monroewilliams/trackball/pictures/prototype-1.jpeg

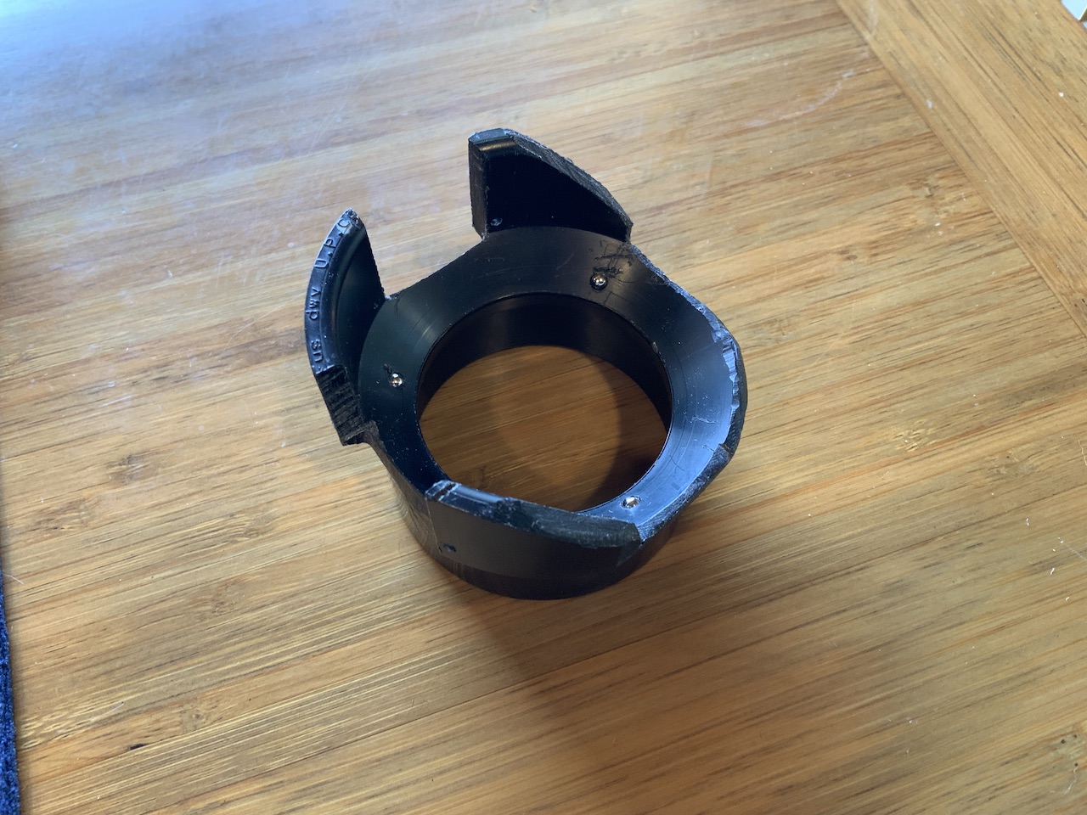
pictures/prototype-1.jpeg
