monroewilliams/trackball/hardware/trackball.scad

// This module prints the full trackball body, with all cutouts.
// full();

// This prints the bottom plate. To use it, comment out full() above and uncomment this line.
// The first argument is the thickness of the bottom cover in mm. I recommend at least 3, for structural integrity.
// The second argument controls whether the bottom cover includes the shape of the button supports.
// The third argument controls whether the attachment pins have screw holes for M3 countersunk machine screws.
//    This can be useful if the friction fit on the pins isn't holding well.
// bottom_cover(3, false, true);

////////////////////
// This selects the ball size.
// A regulation billiard ball is 2 1/4" (~57mm) in diameter.
// ball_diameter=57;

// Ball from the Kensington Slimblade is 55mm.
ball_diameter=55;

// A regulation snooker ball is 52.5mm (~2 1/16").
// The ball from a Trackman Marble FX is 52.33mm by my caliper
// The ball from an Elecom HUGE is 51.97mm by my caliper.
// ball_diameter=52.5;


////////////////////
// sensor_params sets the location and type of the sensors.
// Sensor params are:
// 0 - location angle (clockwise from top)
// 1 - sensor needs bottom access cutout (boolean)
// 2 - sensor type -- one of the following:
sensor_type_adns9800 = 0;
sensor_type_pmw3360 = 1;

sensor_params = [
    [180, true, sensor_type_pmw3360],
    [45, true, sensor_type_pmw3360]
];

////////////////////
// At one point, I found that having sensors directly face-on to the ball didn't work.
// This may have been due to some interaction between the ADNS9800 and the particular ball I was using.
// Setting this to 10 fixes the issues with that sensor/ball combination.
// With the pmw3360 and one of the purpose-made balls (Kensington/Perixx), it seems to work fine to have a skew angle of 0.
sensor_skew_angle=0;

// Should the attachment points have voids for screws?
bottom_screws = true;

////////////////////
// My custom designed pmw3360 boards need a little more clearance on the plug side.
// This should be harmless if using the boards from Tindie, but this lets you disable it
custom_pmw3360_clearance=true;

////////////////////
// True to have a cutout on the left side for cabling/access to the breadboard.
// This isn't needed with the new custom board, as the cable can exit to the front.
side_breadboard_cutout=true;

////////////////////
// If using the custom board, breadboard tabs aren't useful.
breadboard_tabs=true;

////////////////////
// This sets the number and location of the cutouts/supports for buttons.
// Button params are:
// 0 - azimuth angle (clockwise from top)
// 1 - elevation angle (downwards from level)
// 2 - distance from ball surface to button center (takes ball radius into account)
// 3 - tilt angle away from ball (additive with elevation angle)
// 4 - tilt angle in the clockwise direction
// 5 - cutout rotation
// 6 - front overhang (should match up with parametrs in microswitch_cherry_mx.scad)
// 7 - rear overhang (same)
// 8 - create bottom access cutout
// 9 - add support
example_button_params = [
    // main button (matches mircroswitch-cherry-mx-5-20.stl)
    [110, 27, 12, -5, 7, -3 - 90, 5, 20, true, false],

    // ring finger button (matches mircroswitch-cherry-mx-5-5.stl)
    [-70, 33, 13, 30, -8, 5, 0, 0, true, true],

    // second thumb button (matches mircroswitch-cherry-mx-20-0.stl)
    [165, 0, 17, 70, 60, 180 + 30, 20, 0, false, false],

    // middle finger button (could use mircroswitch-cherry-mx-5-5.stl or an actual keyswitch)
    [-25, 20, 17, -15, 30, 0, 0, 0, true, true],

    // index finger button (could use mircroswitch-cherry-mx-5-5.stl or an actual keyswitch)
    [10, -0, 17, 5, 30, 0, 0, 0, true, true],
];

button_params = [
    example_button_params[0],
    example_button_params[1],
    example_button_params[2]
];

////////////////////////////////////////////////////////////////
// Below this line, things get complicated. 

minimal_body_height=1;
minimal_body_diameter=67;

// Bearings are 1/8" == 3.175mm
ball_clearance=1;
bearing_diameter=3.175;

bottom_clearance=4;
hole_diameter=ball_diameter - 25;

bearing_angle=60;
bearing_spacing=[ 
    [0, 0, 0],
    [0, 0, 120],
    [0, 0, -120] 
];

sensor_angle=60;

sensor_clearance=2;
lens_thickness=3.3;
sensor_board_thickness=2;
sensor_board_clearance=0;
        

// Give the ball clearance all the way around in the recess
ball_radius=ball_diameter/2;
recess_radius=ball_radius + ball_clearance;

// Shorthand for the minimum z coordinate
bottom = -(recess_radius + bottom_clearance);

module button_transform(params)
{
    rotate([0, 0, params[0]])
    rotate([-params[1], 0, 0])
    translate([0, ball_radius + params[2], 0])
    rotate(-[params[3], 0, 0])
    rotate([0, params[4], 0])
    rotate([0, 0, params[5]]) 
    children();
}

button_pod_diameter = 20;

module ccube(x, y, z)
{
    translate([0, 0, z/2])
    cube(center=true, [x,y, abs(z)]);
}

module rcube(x, y, z, r)
{
    translate([0, 0, z < 0 ? z : 0])
    linear_extrude(height = abs(z))
    rrect(x, y, r);
}

module rrect(x, y, r)
{
    translate([-x/2, -y/2, 0])
    translate([r, r, 0])
    offset(r)
    square([x - (r * 2), y - (r * 2)]);
}

module prender(convexity = 1)
{
    // Render only in preview mode.
    // Using unconditional render() calls seems to cause my final render to fail

    if ($preview)
    {
        render(convexity)
        children();
    }
    else
    {
        children();
    }
}

module shadow_hull(extra_height = 0)
{
    // This creates an object which is a hull of the object itself and its shadow on the x/y plane.
    hull()
    {
        // the child object
        children();

        // the projection of the child object
        translate([0, 0, bottom - 1 - extra_height]) 
        linear_extrude(height=1)
        projection()
        children();
    }
}

module ball()
{
    color("red")
    sphere(d=ball_diameter);
}

module ball_cutout()
{
    union()
    {
        // spherical part of the recess
        sphere(d=50);
        sphere(d=ball_diameter + (ball_clearance * 2));

        // clearance cut for ball removal, roughly matching the angle of the right front cut
        // The angle here isn't critical, it just needs to not look funny,
        // and not intersect the bearing cutouts (they have very tight tolerances)
        rotate([0, -45 , 30])
        rotate([0, 90, 0])
        cylinder(d=ball_diameter + (ball_clearance), h=ball_diameter);


        // bottom hole
        translate ([0, 0, -100])
        cylinder(h=100, d = hole_diameter);
    }
}

module bearing_cutouts()
{
    union()
    {
        // bearing holes
        for(i = bearing_spacing )
        {
            rotate(i)
            rotate([bearing_angle - 180, 0, 0])
            {
                new_bearing_holes = true;

                // Orginal bearing hole consists of a hemisphere and a straight cylinder.
                hull() 
                {
                    translate ([0,0,ball_radius + (bearing_diameter/2)])
                        sphere (d=bearing_diameter);
                    if (!new_bearing_holes)
                    {
                        // new bearing hole leaves the slight overhang, but makes cuts around it below.
                        translate ([0,0,ball_radius - (bearing_diameter/2)])
                        cylinder (h=bearing_diameter, d=bearing_diameter);
                    }
                }

                if (new_bearing_holes)
                {
                    // relief around the bearing hole - testing a different idea
                    cut_angle = 60;
                    translate([0,0,ball_radius + (bearing_diameter)])
                    for (i = [0, 120, 240])
                    rotate([0, 0, i + 90 - (cut_angle/2)])
                    rotate_extrude(cut_angle)
                    polygon([
                        [0, 0],
                        [0, -bearing_diameter],
                        [-bearing_diameter, -bearing_diameter]
                    ]);
                }

                // through-hole to push out the bearing
                cylinder (h=ball_radius + bearing_diameter + 100, d=2);
            }
        }
    }
}

module button_cutout(front_overhang = 0, rear_overhang = 0)
{
    union() 
    {
        translate([0, 0, -10])
        {
            // the hole the switch fits into
            ccube(14, 14, 20);
        }

        if ((front_overhang == 0) && (rear_overhang == 0))
        {
            // 3mm cut around the hole for seating/overhang and keycap
            rcube(20, 20, 20, 1);
        }
        else
        {
            // 1mm cut around the hole for seating/overhang
            ccube(16, 16, 20);
        }

        // Front and rear overhangs are intended to match up with the overhang parameters in 
        // microswitch-cherry-mx.scad.
        if (front_overhang > 0)
        {
            // Cutout for the safety catch
            translate([-7.5, 7, 0])
            cube([15, 5, 20]);
            // Cutout for the part of the top which extends past the catch
            translate([-7.5, 7, 4])
            cube([15, front_overhang + 3, 16]);
        }

        if (rear_overhang > 0)
        {
            translate([-7.5, -7 - (1 + rear_overhang), 0])
            cube([15, 1 + rear_overhang, 20]);
        }
    }
}

module button_access_base()
{
    translate([0, 0, -10])
    {
        ccube(14, 14, 1);
    }
}


adns9800_board_radius = 32;

// The pmw3360 board is 28mm wide, but the lens assembly is not quite centered on it.
// Either offset it slightly with pmw3360_board_offset or add a little extra width
// and let the size of the holes take up the slop.
pmw3360_board_width = 28 + 1;
pmw3360_board_offset = 0;
pmw3360_board_height = 21 + 1;
pmw3360_lens_radius = 7;
pmn3360_curved_top_scale = 0.25;

module sensor_screw_hole()
{
    // the screw hole
    translate([0, 0,-4])
    color("white", 0.5)
    // my original unknown-source self-tapping screws
    // cylinder(d=1.5, h=10);
    // 2mm machine screws
    cylinder(d=2, h=10);


    // screwdriver access
    translate([0, 0,-104])
    color("white", 0.5)
    cylinder(d=3, h=100);
}

module pmw3360_board()
{
    z = sensor_board_thickness + sensor_board_clearance;
    if (custom_pmw3360_clearance)
    {
        // Outline of the custom sensor board
        // a polygon with the shape of the new board
        x = pmw3360_board_width / 2;
        y = pmw3360_board_height / 2;
        color("green", 0.5)                     
        linear_extrude(height = z, center = false)
        polygon([
            [-x, -y],
            [-x, y],
            [x, y],
            [x, -y],
            [7, -y],
            [5.5, -(y + 2)],
            [-5.5, -(y + 2)],
            [-7, -y],
        ]);
    } else {
        // The board itself (original)
        color("green", 0.5) ccube(pmw3360_board_width, pmw3360_board_height, z);
    }
}

module sensor_cutout(params)
{
    if (params[2] == sensor_type_adns9800)
    {
        union()
        {
            // origin of the sensor is at the surface of the lens, 
            // with the lens facing towards +z, and the "top" of the sensor (where the wires exit) towards +y
        
            // window portion of lens is roughly 11x9mm. This will make a window.
            color("white", 0.25)
            hull()
            {
                rcube(11, 9, 6, 2);
                // round the top to reduce bridging
                translate([0, 2.5, 0])
                scale([1, 0.5, 1])
                cylinder(d=11, h=6);
            }
                        
            // Lens portion of sensor is 22 x 20 mm, centered on the board
            color("gray", 0.5)
            intersection()
            {
                ccube(22,adns9800_board_radius, -(lens_thickness + 1));
                translate([0, 0, -(lens_thickness + 2)])
                cylinder(d=adns9800_board_radius, h=lens_thickness + 3);
            }
        
            // the board is a 32mm circle, ~2mm thick.
            // Add some thickness to the back to leave room for components, etc.
            z = sensor_board_thickness + sensor_board_clearance;
            translate([0,0,-(lens_thickness + z)])
            {
                // The board itself
                color("green", 0.5) cylinder(d=adns9800_board_radius, h=z);
                
                // Hemisphere for clearance
                difference()
                {
                    color("white", 0.25)
                    sphere(d=adns9800_board_radius);
                    
                    translate([0,0,1])
                    cylinder(d=adns9800_board_radius, h=17);
                }
            }
            
            // The screws are 27mm apart, on the centerline of the board.
            screw_distance=27;
            for(i = [ screw_distance/2,
                    -screw_distance/2 ] )
            {
                translate([i, 0, 0])
                sensor_screw_hole();
            }
        }
    }
    else if(params[2] == sensor_type_pmw3360)
    {
        union()
        {
            // origin of the sensor is at the surface of the lens, 
            // with the lens facing towards +z, and the "top" of the sensor (where the wires exit) towards +y
        
            // window portion of lens is roughly 11x9mm. This will make a window.
            color("white", 0.25)
            hull()
            {
                rcube(11, 9, 6, 2);
                // round the top to reduce bridging
                translate([0, 2.5, 0])
                scale([1, 0.5, 1])
                cylinder(d=11, h=6);
            }
            
            // Lens portion of sensor is 21.2 x 19 mm
            color("gray", 0.5)
            intersection()
            {
                rcube(22, 20, -(lens_thickness + 1), pmw3360_lens_radius);
                // translate([0, 0, -(lens_thickness + 2)])
                // cylinder(d=32, h=lens_thickness + 3);
                
            }

            // The board is shifted slightly relative to the lens
            translate([pmw3360_board_offset, 0, 0])
            {
                // leave room for the wire solder joints on the lens side
                // color("white", 0.25)
                translate([0, pmw3360_board_height/2, ])
                {
                    hull()
                    {
                        translate([0, -2, 0])
                        ccube(pmw3360_board_width, 4, -(lens_thickness + 1));

                        // Curved cut above the board to reduce bridging
                        translate([0, 0, -(lens_thickness)])
                        scale([1, pmn3360_curved_top_scale, 1])
                        cylinder(d=pmw3360_board_width, h=0.1);
                    }
                }

                // the board is a 28mm x 21mm rectangle, ~2mm thick.
                // Add some thickness to the back to leave room for components, etc.
                z = sensor_board_thickness + sensor_board_clearance;
                translate([0,0,-(lens_thickness + z)])
                {
                    pmw3360_board();

                    hull()
                    {
                        // Curved cut above the board to reduce bridging
                        color("white", 0.25)
                        translate([0, pmw3360_board_height/2, z])
                        scale([1, pmn3360_curved_top_scale, 1])
                        cylinder(d=pmw3360_board_width, h=0.1);
                        
                        // backside clearance (half cylinder)
                        difference()
                        {
                            color("white", 0.25)
                            rotate([0, 90, 0])
                            cylinder(center = true, d=pmw3360_board_height, h=pmw3360_board_width);
                            
                            translate([0,0,1])
                            ccube(pmw3360_board_width + 2, pmw3360_board_height + 2, 17);
                        }
                    }
                }
                
                // The screws are 24mm apart, on the centerline of the board.
                screw_distance=24;
                for(i = [ screw_distance/2,
                        -screw_distance/2 ] )
                {
                    translate([i, 0, 0])
                    sensor_screw_hole();
                }
            }
        }
    }
}

module sensor_access_base(params)
{
    // This is just the backside model, used to create an access hole.
    if (params[2] == sensor_type_adns9800)
    {
        // the board is a 32mm circle, ~2mm thick.
        // Add some thickness to the back to leave room for components, etc.
        z = sensor_board_thickness + sensor_board_clearance;
        translate([0,0,-(lens_thickness + z)])
        {
            // The board itself
            cylinder(d=adns9800_board_radius, h=z);
            
            // Hemisphere for clearance
            difference()
            {
                sphere(d=adns9800_board_radius);
                
                translate([0,0,1])
                cylinder(d=adns9800_board_radius, h=17);
            }
        }
    }
    else if(params[2] == sensor_type_pmw3360)
    {
        // the board is a 28mm x 21mm rectangle, ~2mm thick.
        // Add some thickness to the back to leave room for components, etc.
        z = sensor_board_thickness + sensor_board_clearance;
        translate([0,0,-(lens_thickness + z)])
        {
            // The board is shifted slightly relative to the lens
            translate([pmw3360_board_offset, 0, 0])
            {
                // The board itself
                pmw3360_board();
                // color("green", 0.5) ccube(pmw3360_board_width, pmw3360_board_height, z);
                
                hull()
                {
                    // Curved cut above the board to reduce bridging
                    color("white", 0.25)
                    translate([0, pmw3360_board_height/2, z])
                    scale([1, pmn3360_curved_top_scale, 1])
                    cylinder(d=pmw3360_board_width, h=0.1);

                    // backside clearance (half cylinder)
                    difference()
                    {
                        color("white", 0.25)
                        rotate([0, 90, 0])
                        cylinder(center = true, d=pmw3360_board_height, h=pmw3360_board_width);
                        
                        translate([0,0,1])
                        ccube(pmw3360_board_width + 2, pmw3360_board_height + 2, 17);
                    }
                }
            }
        }
    }
}

module sensor_shell(params)
{
    // A solid which completely encloses the sensor cutout/access cutout,
    // so it can be protected from the top.

    if (params[2] == sensor_type_adns9800)
    {
        // This is essentially the sphere defined by sensor_access_base, expanded by 2mm.
        z = sensor_board_thickness + sensor_board_clearance;
        translate([0,0,-(lens_thickness + z)])
        {
            sphere(d=adns9800_board_radius + 4);
        }
    }
    else if(params[2] == sensor_type_pmw3360)
    {
        // The backside clearance half-cylinder, extended to a full cylinder, and made 2mm larger
        z = sensor_board_thickness + sensor_board_clearance;
        translate([0,0,-(lens_thickness + z)])
        {
            // The board is shifted slightly relative to the lens
            translate([pmw3360_board_offset, 0, 0])
            {
                hull()
                {
                    // Curved cut above the board to reduce bridging
                    translate([0, 2 + pmw3360_board_height/2, z])
                    scale([1, pmn3360_curved_top_scale, 1])
                    cylinder(d=4 + pmw3360_board_width, h=0.1);

                    rotate([0, 90, 0])
                    cylinder(center = true, d=pmw3360_board_height + 4, h=pmw3360_board_width + 4);
                }
            }
        }
    }
}

module sensorpod(params)
{
    rotate([sensor_angle, 0, 0])
    translate([0, 0, -(lens_thickness + ball_radius + sensor_clearance)]) 
    {
        rotate([sensor_skew_angle, 0, 0])
        {
            if (params[2] == sensor_type_adns9800)
            {
                difference()
                {
                    cylinder(d=adns9800_board_radius, h=lens_thickness);
                    
                    translate([-17, 2, 0]) 
                    cube([adns9800_board_radius + 2, 20, lens_thickness]);
                }
            }
            else if(params[2] == sensor_type_pmw3360)
            {
                // The board is shifted slightly relative to the lens
                translate([pmw3360_board_offset, 0, 0])
                {
                    ccube(pmw3360_board_width, pmw3360_board_height, lens_thickness);
                }
            }
        }
    }
}

breadboard_size = [46.5, 34.75, 9.5];
breadboard_offset = [-5, -(ball_radius + 21.5)];

module breadboard_tab()
{
    hull()
    {
        ccube(5.0, 5.0, 6.5);
        translate([0, 0, 6.5])
        sphere(d=4);
    }
}

module breadboard_cutout()
{
    union()
    {
        // main body
        ccube(breadboard_size[0], breadboard_size[1], breadboard_size[2]);

        // clearance cutout
        intersection()
        {
            // ccube(breadboard_size[0], breadboard_size[1], 200);
            linear_extrude(height=80, scale=1.0)
            square(center=true, [breadboard_size[0], breadboard_size[1]]);

            // Tweak the location of the top of the cutout to make it a reasonable shell
            // Note that any adjustment to the body shape may require adjusting this.
            translate([4.0, 2.0, -4.0])
            translate([-breadboard_offset[0], -breadboard_offset[1], -bottom])
            body();

        }

        if (breadboard_tabs)
        {
            // connection tabs
            translate([0, breadboard_size[1] / 2, 0])
            breadboard_tab();
            translate([0, -breadboard_size[1] / 2, 0])
            breadboard_tab();
            translate([breadboard_size[0] / 2, 0, 0])
            breadboard_tab();
            translate([-breadboard_size[0] / 2, 0, 0])
            breadboard_tab();
        }

        if (side_breadboard_cutout)
        {
            // USB Cable clearance
            translate([0, 0, 4])
            rotate([0, -100, 0])
            cylinder(d=breadboard_size[1], h=50);
        }
    }
}

module breadboard_clearance()
{

}

module body_left_cut(inner_fillet = 20, outer_fillet = 0)
{
    union()
    {
        rotate([-10, 0, 10])
        translate ([3- ball_radius, 0, bottom])
        {
            radius = 120;
            downward_curve = 40;
            ledge_height = 20;
            // translate([radius, 0, -radius])
            // cylinder(r=radius, h=radius * 2);

            translate([0, 0, ledge_height])
            rotate([0, downward_curve, 0])
            translate([radius, 0, -ledge_height])
            rotate([0, 0, 90])
            rotate_extrude(angle=180)
            intersection()
            {
                union()
                {
                    // fillet
                    fillet_amount = 20;
                    offset(outer_fillet)
                    offset(-(inner_fillet + outer_fillet))
                    offset(inner_fillet)
                    translate([radius, ledge_height])
                    rotate([0, 0, -downward_curve])
                    translate([-radius, -ledge_height])
                    union()
                    {
                        // upright wall
                        translate([-100, -100])
                        square([100 + radius, 200]);

                        // ledge
                        translate([radius, ledge_height])
                        rotate([0, 0, -15])
                        translate([-radius, -ledge_height])
                        translate([0, -100])
                        square([radius + 25, 100 + ledge_height]);

                        // Make outside edge vertical
                        translate([0, -107])
                        square([radius + 25, 100 + ledge_height]);

                    }

                    // offset(fillet_amount)
                    // offset(-fillet_amount) 
                    // square([50, 50]);
                }
                // Clip to positive X
                translate([0, -150])
                square([300, 300]);
            }
        }  
        // Don't cut anything aft of tail_y_boundary with this shape.
        // translate([-100, -200 + tail_y_boundary, -100])
        // cube([200, 200, 200]);
    }
}

module body_right_front_cut()
{
    scale([0.89, 0.9, 0.815])
    rotate([0, 0, 90])
    rotate_extrude(angle=-180)
    intersection()
    {
        // scale([0.8, 0.6])
        circle(r=100);

        // Clip to positive X
        translate([0, 0])
        square([300, 300]);
    }
}

module body_right_rear_cut_template(params)
{
    // Match the front right cut at the intersection point at the z=0 plane
    rotate([-params[2], 0, 0])
    scale([1, 1, 1.0 / params[3]])
    rotate([-90, 0, 0])
    {
        translate([-params[0], -params[1], 0])
        body_right_front_cut();
    }

}

module body_right_rear_cut(params)
{
    translate([params[0], params[1], 0])
    scale([1.0, params[3], 1.0])
    rotate([-params[2], 0, 0])
    union()
    {
        rotate_extrude()
        intersection()
        {  
            offset(-params[6]) 
            offset(params[6])
            union()
            {
                // Match the front right cut at the intersection point
                projection(cut=true)
                body_right_rear_cut_template(params);

                // add the horizontal base
                rotate([0, 0, -(params[2] + params[4])])
                translate([0, -100 + params[5]])
                square([250, 100]);
            }

            // Clip to positive X
            translate([0, -150])
            square([300, 300]);
        }
        
        // Don't clip forward of this part
        translate([-200, 0, -200])
        cube([400, 400, 400]);
    }
}

module body_right_cut_translation()
{
    y_translation_angle = -45;
    z_translation_angle = 40;
    translation_amount = 80 - ball_diameter / 4;

    rotate([0, -y_translation_angle, 0])
    rotate([0, 0, -z_translation_angle])
    translate([0, 0, -translation_amount])
    rotate([0, 0, z_translation_angle])
    rotate([0, y_translation_angle, 0])
    translate([0, -30, 0])
    children();
}

// right rear shape params are:
// 0 - x offset
// 1 - y offset
// 2 - saddle rotation angle
// 3 - y scaling
// 4 - horizontal component angle (added to saddle angle)
// 5 - horizontal component height
// 6 - fillet amount
// right_rear_params = [20, 0, 35, 0.6, 5.0, 26, 60];
// right_rear_params = [20, 0, 27, 0.7, 7.5, 30, 90];
right_rear_params = [21, 2, 25, 0.7, 8, 30, 90];
// Settings roughly equivalent to previous:
// right_rear_params = [28, 0, 0, 0.7, 5.1, 22.5, 70];
module body_right_cut()
{
    body_right_cut_translation()
    intersection()
    {
        union()
        {
            body_right_front_cut();

            // Don't cut left of the center point
            translate([-200, 0, 0])
            cube([200, 200, 200]);

            // and don't cut off the tail tip
            // translate([-100, -200 - 50, -100])
            // cube([200, 200, 200]);
        }
        union()
        {
            body_right_rear_cut(right_rear_params);
        }

    }
}

module body_button_supports()
{
    for(i = button_params )
    {
        if(i[9])
        {
            shadow_hull(10)
            button_transform(i)
            translate([0, 0, -10])
            rcube(20, 20, 10, 3);
        }
    }
}


module body(include_button_supports = true, include_sensor_shells = true)
{
    intersection()
    {
        // Clip to above bottom surface
        translate ([0, 0, bottom])
        ccube(400, 400, 400);

        body_unclipped(include_button_supports, include_sensor_shells);
    }

}
module body_unclipped(include_button_supports = true, include_sensor_shells = true)
{
    difference()
    {
        union()
        {
            intersection()
            {
                // left cut
                body_left_cut();
                        
                // right cut
                body_right_cut();
            }        
 
            if (include_button_supports)
            {
                body_button_supports();
            }

            if (include_sensor_shells)
            {
                sensor_shells();
            }
        }

        // Trim the front of the body so it's not pointy for no reason
        rotate([0, 0, 45])
        translate([0, 100, -100 + bottom])
        ccube(100, 100, 200);
    }
}

stud_diameter = 5;
stud_height = 2;

module bottom_stud()
{
    translate([0, 0, -0.01])
    cylinder(d=stud_diameter, h = stud_height + 0.01);
}

module bottom_stud_screw_hole()
{
    // Add a hole that can be used for an M3x8 countersunk screw, for more permanent installs.
    translate([0, 0, 2])
    {
        cylinder(d=3, h = 10);

        mirror([0, 0, 1])
        {
            linear_extrude(height=2, scale=2)
            circle(d=3);

            translate([0, 0, 2])
            linear_extrude(height=10)
            circle(d=6);
        }
    }
}


 module circle_outer(radius,fn)
 {
   fudge = 1/cos(180/fn);
   circle(r=radius*fudge,$fn=fn);
}

module bottom_stud_hole()
{
    union()
    {
        // Polygonal, circumcribed hole.
        hole_sides = 8;
        translate([0, 0, -0.01])
        linear_extrude(height=stud_height+0.02)
        circle_outer(stud_diameter/2, hole_sides);

        // Taper to a point for easier printing
        translate([0, 0, stud_height])
        linear_extrude(height=stud_diameter / 2, scale=0)
        circle_outer(stud_diameter/2, hole_sides);

        if (bottom_screws)
        {
            // Add a hole that can be used for an M3x8 countersunk screw, for more permanent installs.
            // height is the screw depth minus the bottom thickness.
            cylinder(d=3, h=6);
        }
    }
}

stud_locations = [
    // Clockwise when looking at the bottom of the body, starting from the tail.
    [0, -80],
    // Moving this one a bit due to clearance issues between the top surface and the mounting screw hole.
    // [25, -65],
    [27, -55],
    [33, -20],
    [-4, 23],
    [-45, 15],
    [-39, -27],
];

module bottom_cover(thickness = 3, include_button_supports = false, include_screw_holes = false)
{
    difference()
    {
        union()
        {
            intersection()
            {
                translate([0, 0, - bottom])
                {
                    difference()
                    {
                        body_unclipped(include_button_supports);
                        ball_cutout();
                    }
                }
                ccube(400, 400, -thickness);
            }

            for(i = stud_locations)
            {
                translate(i)
                bottom_stud();
            }
        }

        if (include_screw_holes)
        {
            for(i = stud_locations)
            {
                translate(i)
                translate([0, 0, -thickness])
                bottom_stud_screw_hole();
            }
        }
    }
}

module stud_hole_cutouts()
{
    for(i = stud_locations)
    {
        translate([i[0], i[1], bottom])
        bottom_stud_hole();
    }
}

module body_minimal()
{
    intersection()
    {
        // Clip to above bottom surface
        translate ([0, 0, bottom])
        ccube(400, 400, 400);
        difference()
        {
            // Main body
            union()
            {
                hull()
                {
                    // Footprint outline
                    translate ([0, 0, -(recess_radius + bottom_clearance)])
                    cylinder(h=minimal_body_height, d=minimal_body_diameter);
                    
                    // Pods for each of three support bearings
                    for(i = bearing_spacing )
                    {
                        rotate(i) 
                        rotate([bearing_angle, 0, 0])
                        translate([0, 0, -(ball_radius + (bearing_diameter/2))]) 
                        scale([1, 1, 0.5])
                        sphere(r=5);
                    }
                            
                    // Pods for two sensors
                    for(i = sensor_params )
                    {
                        rotate(i[0])
                        sensorpod(i);
                    }

                    // Button pods
                    for(i = button_params )
                    {
                        shadow_hull()
                        button_transform(i)
                        translate([0, 0, -10])
                        cylinder(h=10, d=button_pod_diameter);
                    }
                }
            }
        }
    }
}

wire_channel_size = 10;
wire_channel_primary_radius = ball_radius - 3.5;

module wire_cutout_profile()
{
    rotate([0, 0, 45])
    rrect(wire_channel_size, wire_channel_size, 2);
    // circle(d=wire_channel_size, $fn=30);
}

module wire_cutout_straight_section(h)
{
    translate([0, 0, -0.01])
    union()
    {
        linear_extrude(height = h)
        wire_cutout_profile();
        translate([0, 0, h])
        sphere(r=wire_channel_size * 1.5);
        // linear_extrude(height = 8, scale=2)
        // wire_cutout_profile();
    }
}

module wire_cutouts()
{
    translate([0, 0, bottom])
    union()
    {
        if(false)
        {
            // segment just to the front sensor
            // rotate([0, 0, 180 + 10])
            // translate([wire_channel_primary_radius, 0, 0])
            // rotate([90, 0, 0])
            // translate([0, 0, -0.01])
            // linear_extrude(20)
            // wire_cutout_profile();

            // rotate([0, 0, 180 + 10])
            // rotate_extrude(angle=25)
            // translate([wire_channel_primary_radius, 0, 0])
            // wire_cutout_profile();
        }
        else
        {
            // most of a full circle
            rotate([0, 0, 180 - 45])
            rotate_extrude(angle=75)
            translate([wire_channel_primary_radius, 0, 0])
            wire_cutout_profile();
        }

        rotate([0, 0, 180 + 30])
        translate([wire_channel_primary_radius, 0, 0])
        rotate([-90, 0, 0])
        wire_cutout_straight_section(20);

        rotate([0, 0, -30])
        translate([wire_channel_primary_radius, 0, 0])
        rotate([90, 0, 0])
        wire_cutout_straight_section(20);

        rotate([0, 0, -35])
        rotate_extrude(angle=63)
        translate([wire_channel_primary_radius, 0, 0])
        wire_cutout_profile();

        // Access out the front for the USB cable.
        // Match the radius of the outer edge.
        secondary_radius = 70;
        rotate([0, 0, 27])
        translate([wire_channel_primary_radius - secondary_radius, 0, 0])
        rotate_extrude(angle=55)
        translate([secondary_radius, 0, 0])
        wire_cutout_profile();

        // Room for the breadboard under the handrest
        translate([breadboard_offset[0], breadboard_offset[1], 0])
        breadboard_cutout();
    }

}

module sensor_transform(params)
{
    rotate([0, 0, params[0]])
    rotate([sensor_angle, 0, 0])
    translate([0, 0, -(ball_radius + sensor_clearance)]) 
    rotate([sensor_skew_angle, 0, 0])
    children();
}

module sensor_cutouts()
{
    for(params = sensor_params )
    {
        difference()
        {
            sensor_transform(params)
            sensor_cutout(params);
            
            // // Clip the cutouts to the top of the base ring.
            // translate([0, 0, minimal_body_height + bottom])
            // ccube(100, 100, -100);
        }
    }
}

module sensor_access_cutouts()
{
    for(params = sensor_params )
    {
        if (params[1])
        {
            // Bottom access cutout
            shadow_hull()
            sensor_transform(params)
            sensor_access_base(params);
        }
    }
}

module sensor_shells()
{
    for(params = sensor_params )
    {
        difference()
        {
            shadow_hull()
            sensor_transform(params)
            sensor_shell(params);
        }
    }
}


module button_cutouts()
{
    for(params = button_params )
    {
        // cutout for the button itself
        button_transform(params)
        button_cutout(params[6], params[7]);

        if (params[8])
        {
            // Bottom access cutout for the button
            shadow_hull()
            button_transform(params)
            button_access_base();
        }

    }
}

// Set this to 4 for medium-res, 1 for high-res
//$fa = 1;
$fa = 1;
$fs = 0.01;

module full()
{
    intersection() 
    {
        difference()
        {
            body();
            ball_cutout();
            bearing_cutouts();
            sensor_cutouts();
            sensor_access_cutouts();
            button_cutouts();
            wire_cutouts();
            stud_hole_cutouts();
        }

        // Isolate bearing hole for testing purposes
    //    translate([0, 20, -10]) cube(center = true, [10, 20, 20]);
    }
}
