monroewilliams/trackball/stl/bottom_cover_3mm-52.5mm.scad

include <../hardware/trackball.scad>

ball_diameter=52.5;

bottom_cover(3, false, true);
