monroewilliams/trackball/stl/bottom_cover_3mm-55mm.scad

include <../hardware/trackball.scad>


bottom_cover(3, false, true);
