monroewilliams/trackball/stl/bottom_cover_3mm-57mm.scad

include <../hardware/trackball.scad>

ball_diameter=57;

bottom_cover(3, false, true);
