monroewilliams/trackball/stl/microswitch-cherry-mx-20-0.scad

use <../hardware/microswitch-cherry-mx.scad>

switch_carrier(5, 20);
