monroewilliams/trackball/stl/microswitch-cherry-mx-5-20.scad

use <../hardware/microswitch-cherry-mx.scad>

switch_carrier(20, 0);
