monroewilliams/trackball/stl/microswitch-cherry-mx-5-5.scad

use <../hardware/microswitch-cherry-mx.scad>

switch_carrier(5, 5);
