monroewilliams/trackball/stl/microswitch-v2-20-0-14.scad

include <../hardware/microswitch-v2.scad>

switch_carrier(20, 0, 14);
