monroewilliams/trackball/stl/microswitch-v2-5-20-14.scad

include <../hardware/microswitch-v2.scad>

switch_carrier(5, 20, 14);
