monroewilliams/trackball/stl/trackball-52.5mm-pmw3360-hollow.scad

include <../hardware/trackball-hollow.scad>

ball_diameter=52.5;

// One of the screw holes sticks through the top at this size, so just skip them.
bottom_screws = false;

full_hollow();
