monroewilliams/trackball/stl/trackball-55mm-pmw3360-hollow.scad

include <../hardware/trackball-hollow.scad>

ball_diameter=55;

full_hollow();
