monroewilliams/trackball/stl/trackball-57mm-pmw3360-hollow.scad

include <../hardware/trackball-hollow.scad>

ball_diameter=57;

full_hollow();
