monroewilliams/trackball/src/PMW3360DM_firmware.h

// the firmeware that is uploaded in the ADNS each time it boots

#include <avr/pgmspace.h>

// Firmware "PMW3360DM_srom_0x04" from https://github.com/mrjohnk/PMW3360DM-T2QU/blob/master/Arduino%20Examples/PMW3360DM-Interrupt/SROM_0x04_Arduino.ino

const unsigned short firmware_length_pmw3360dm = 4094;

const unsigned char firmware_data_pmw3360dm[] PROGMEM = {
0x01, 0x04, 0x8e, 0x96, 0x6e, 0x77, 0x3e, 0xfe, 0x7e, 0x5f, 0x1d, 0xb8, 0xf2, 0x66, 0x4e, 
0xff, 0x5d, 0x19, 0xb0, 0xc2, 0x04, 0x69, 0x54, 0x2a, 0xd6, 0x2e, 0xbf, 0xdd, 0x19, 0xb0, 
0xc3, 0xe5, 0x29, 0xb1, 0xe0, 0x23, 0xa5, 0xa9, 0xb1, 0xc1, 0x00, 0x82, 0x67, 0x4c, 0x1a, 
0x97, 0x8d, 0x79, 0x51, 0x20, 0xc7, 0x06, 0x8e, 0x7c, 0x7c, 0x7a, 0x76, 0x4f, 0xfd, 0x59, 
0x30, 0xe2, 0x46, 0x0e, 0x9e, 0xbe, 0xdf, 0x1d, 0x99, 0x91, 0xa0, 0xa5, 0xa1, 0xa9, 0xd0, 
0x22, 0xc6, 0xef, 0x5c, 0x1b, 0x95, 0x89, 0x90, 0xa2, 0xa7, 0xcc, 0xfb, 0x55, 0x28, 0xb3, 
0xe4, 0x4a, 0xf7, 0x6c, 0x3b, 0xf4, 0x6a, 0x56, 0x2e, 0xde, 0x1f, 0x9d, 0xb8, 0xd3, 0x05, 
0x88, 0x92, 0xa6, 0xce, 0x1e, 0xbe, 0xdf, 0x1d, 0x99, 0xb0, 0xe2, 0x46, 0xef, 0x5c, 0x07, 
0x11, 0x5d, 0x98, 0x0b, 0x9d, 0x94, 0x97, 0xee, 0x4e, 0x45, 0x33, 0x6b, 0x44, 0xc7, 0x29, 
0x56, 0x27, 0x30, 0xc6, 0xa7, 0xd5, 0xf2, 0x56, 0xdf, 0xb4, 0x38, 0x62, 0xcb, 0xa0, 0xb6, 
0xe3, 0x0f, 0x84, 0x06, 0x24, 0x05, 0x65, 0x6f, 0x76, 0x89, 0xb5, 0x77, 0x41, 0x27, 0x82, 
0x66, 0x65, 0x82, 0xcc, 0xd5, 0xe6, 0x20, 0xd5, 0x27, 0x17, 0xc5, 0xf8, 0x03, 0x23, 0x7c, 
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
0xe2, 0x88, 0x79, 0x37, 0x11, 0x5f, 0x39, 0x89, 0x95, 0x0a, 0x16, 0x84, 0x7a, 0xf6, 0x8a, 
0xa4, 0x28, 0xe4, 0xed, 0x83, 0x80, 0x3b, 0xb1, 0x23, 0xa5, 0x03, 0x10, 0xf4, 0x66, 0xea, 
0xbb, 0x0c, 0x0f, 0xc5, 0xec, 0x6c, 0x69, 0xc5, 0xd3, 0x24, 0xab, 0xd4, 0x2a, 0xb7, 0x99, 
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
